PrintersForAnts/Mini-AfterSherpa/mods/LGXLiteMount/Strain_Relief_Spacers_x2.stl

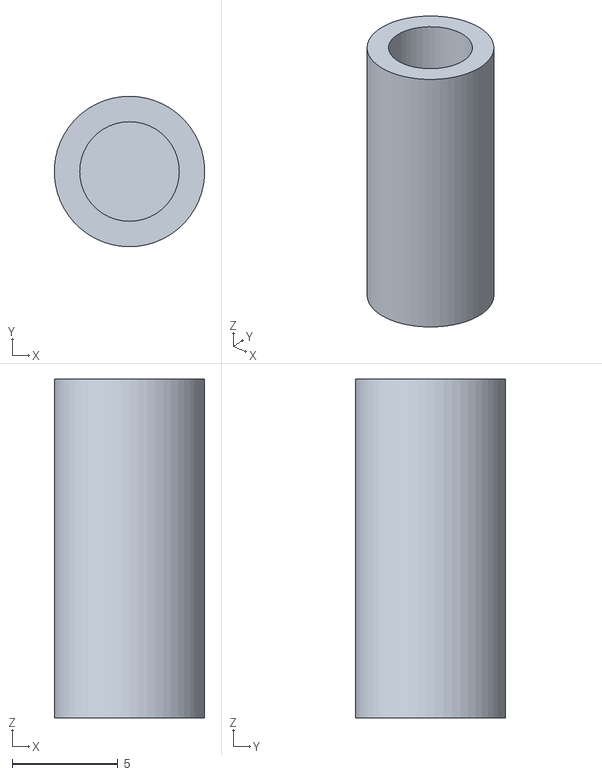
[picture p28: CAD file, 2022-01-24]
mods/LGXLiteMount/Strain_Relief_Spacers_x2.stl
7.09 x 7.10 x 16.0
