PrintersForAnts/Mini-AfterSherpa/STL/Mini_AfterSherpa/E3D_Revo_Micro_Toolhead/MiniAS_Revo_Micro_Shim_V2_x1.stl

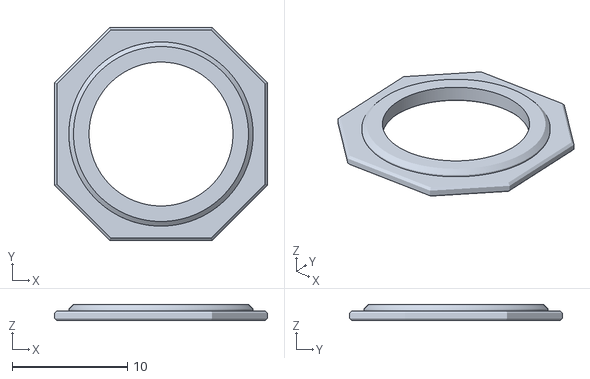
[picture p29: CAD file, 2022-02-25]
STL/Mini_AfterSherpa/E3D_Revo_Micro_Toolhead/MiniAS_Revo_Micro_Shim_V2_x1.stl
18.5 x 18.5 x 1.40
