PrintersForAnts/Mini-AfterSherpa/STL/Mini_AfterSherpa/E3D_V6_Zodiac_BMO_Toolhead/Mount_E3D_V6_x1.stl

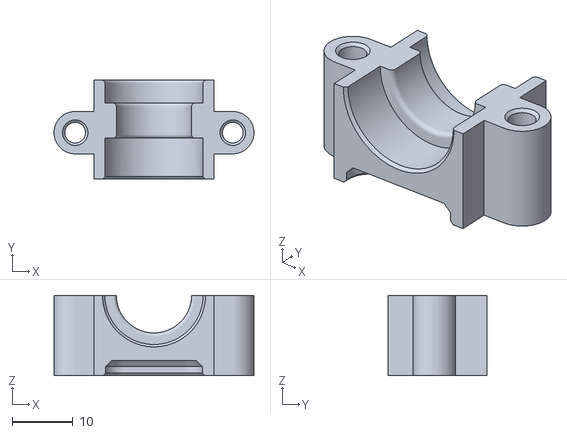
[picture p30: CAD file, 2021-11-07]
STL/Mini_AfterSherpa/E3D_V6_Zodiac_BMO_Toolhead/Mount_E3D_V6_x1.stl
33.0 x 16.4 x 13.3
