PrintersForAnts/Mini-AfterSherpa/STL/Mini_AfterSherpa/MiniAS_Sherpa_Micro_Adapter.stl

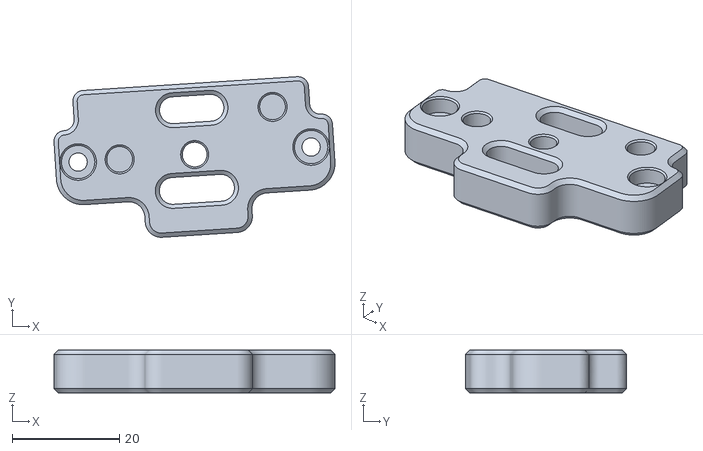
[picture p31: CAD file, 2022-04-30]
STL/Mini_AfterSherpa/MiniAS_Sherpa_Micro_Adapter.stl
52.4 x 29.9 x 8.00
