PrintersForAnts/Mini-AfterSherpa/STL/Mini_AfterSherpa/Orbiter_V2_Toolhead_ONE-OFFS/Mini_AfterSherpa_Orbiter_v2_X_Carriage.stl

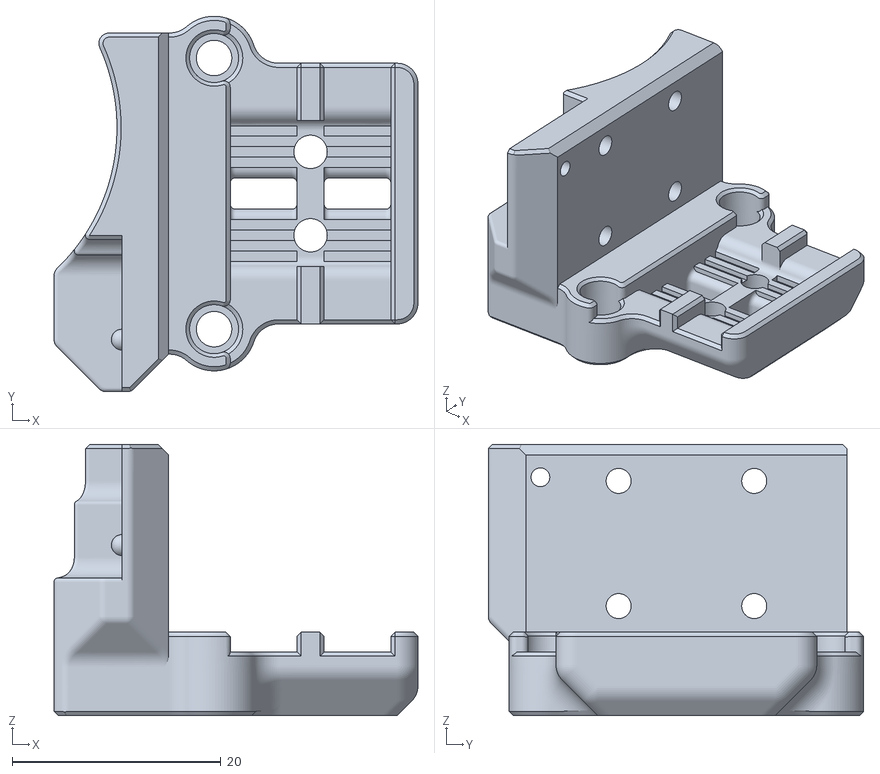
[picture p32: CAD file, 2022-04-30]
STL/Mini_AfterSherpa/Orbiter_V2_Toolhead_ONE-OFFS/Mini_AfterSherpa_Orbiter_v2_X_Carriage.stl
34.9 x 36.0 x 26.0
