PrintersForAnts/Mini-AfterSherpa/STL/Reversed_PocketWatch2/Reversed_Pocketwatch2_Mini_AS_Edition_v0.593/Motor_Mount_Rear_rP2_x1.stl

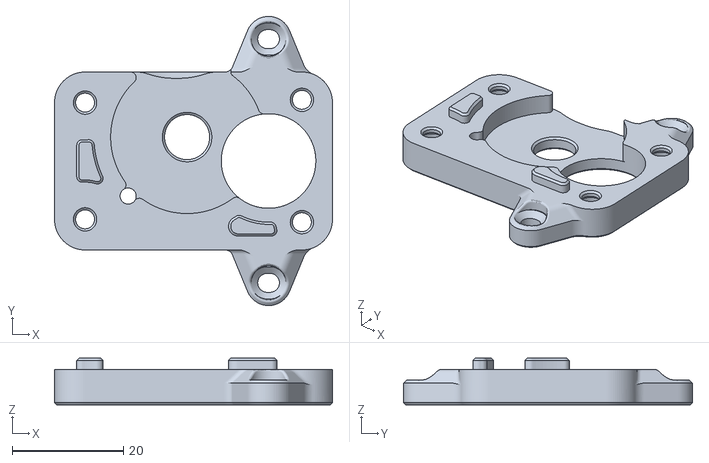
[picture p33: CAD file, 2021-11-07]
STL/Reversed_PocketWatch2/Reversed_Pocketwatch2_Mini_AS_Edition_v0.593/Motor_Mount_Rear_rP2_x1.stl
50.0 x 52.0 x 8.40
