PrintersForAnts/Mini-AfterSherpa/CAD/Mini-AfterSherpa_Zodiac_BMS.step

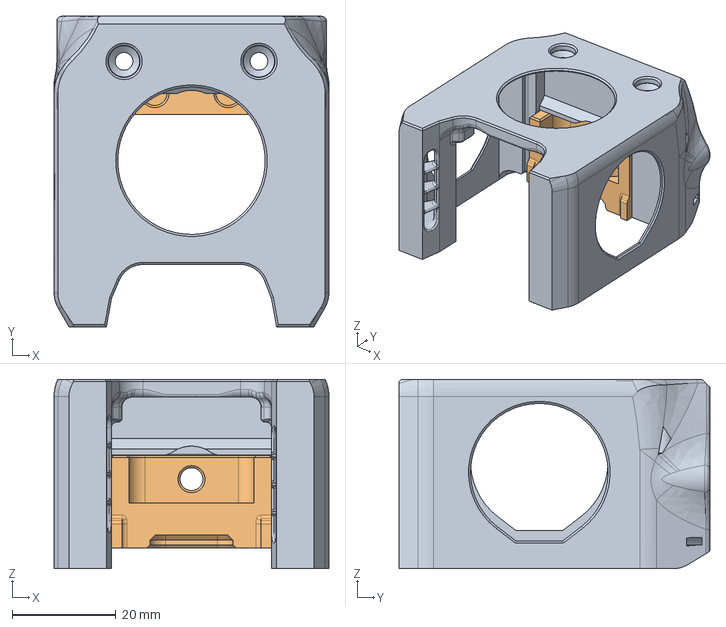
[picture p34: CAD file, 2022-04-30]
CAD/Mini-AfterSherpa_Zodiac_BMS.step
53.0 x 59.9 x 36.5 mm
