PrintersForAnts/Mini-AfterSherpa/mods/LED-Bowden-Adapter/led_logo_diffuser.stl

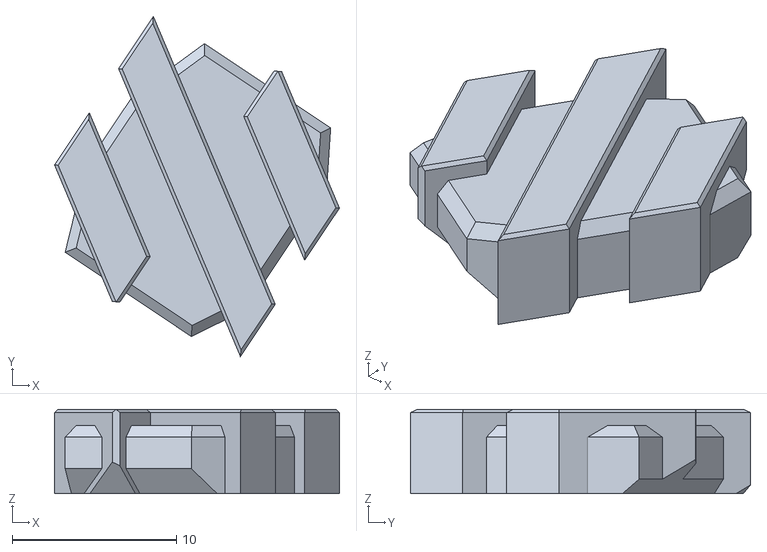
[picture p35: CAD file, 2022-01-20]
mods/LED-Bowden-Adapter/led_logo_diffuser.stl
17.3 x 20.7 x 5.13
