PrintersForAnts/Mini-AfterSherpa/mods/LGXLiteMount/MiniASLGXerpaLite-StrainRelief.stl

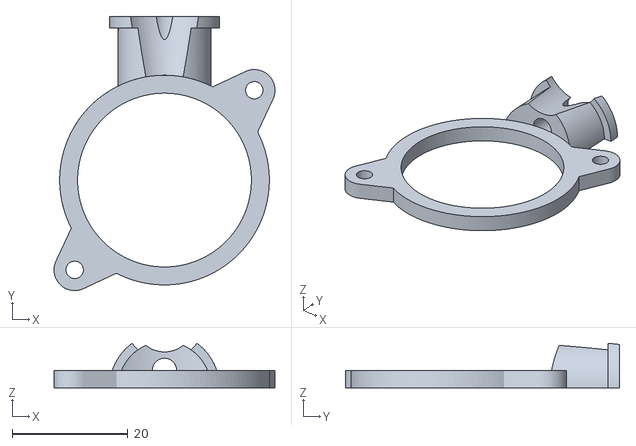
[picture p36: CAD file, 2022-01-24]
mods/LGXLiteMount/MiniASLGXerpaLite-StrainRelief.stl
38.2 x 47.3 x 7.69
