PrintersForAnts/Mini-AfterSherpa/STL/Mini_AfterSherpa/E3D_Revo_Micro_Toolhead/MiniAS_Revo_Micro_Faux_Collet_V2_X1.stl

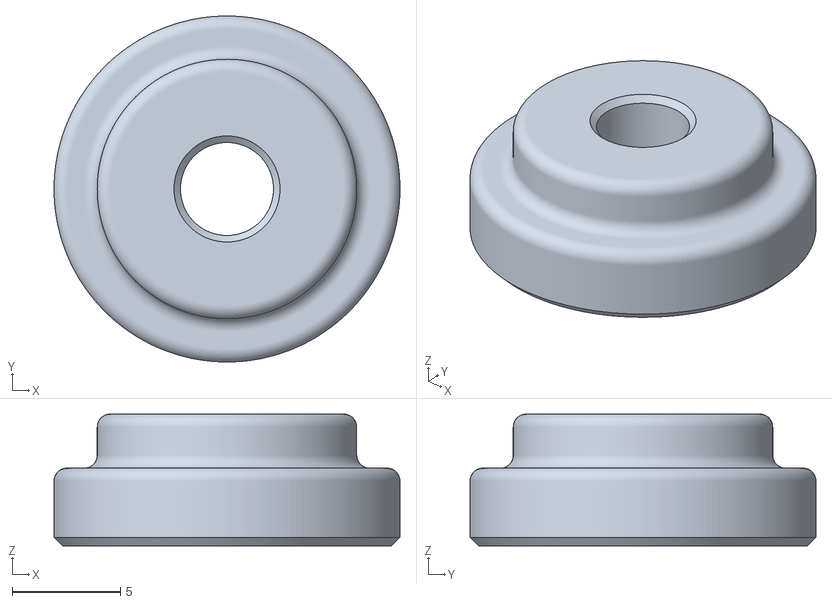
[picture p37: CAD file, 2022-02-25]
STL/Mini_AfterSherpa/E3D_Revo_Micro_Toolhead/MiniAS_Revo_Micro_Faux_Collet_V2_X1.stl
16.0 x 16.0 x 6.10
