PrintersForAnts/Mini-AfterSherpa/STL/Mini_AfterSherpa/MiniAS_Orbiter_v1.5_Adapter.stl

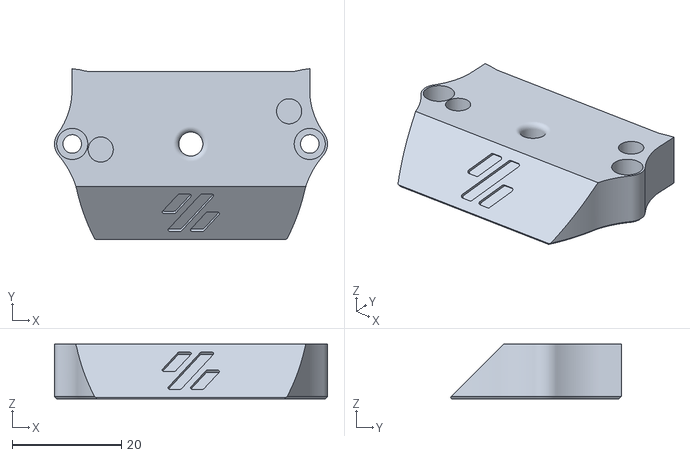
[picture p38: CAD file, 2022-02-27]
STL/Mini_AfterSherpa/MiniAS_Orbiter_v1.5_Adapter.stl
50.0 x 31.3 x 10.0
