PrintersForAnts/Mini-AfterSherpa/STL/Mini_AfterSherpa/Orbiter_V2_Toolhead_ONE-OFFS/Orbiter v2.0 cable support.stl

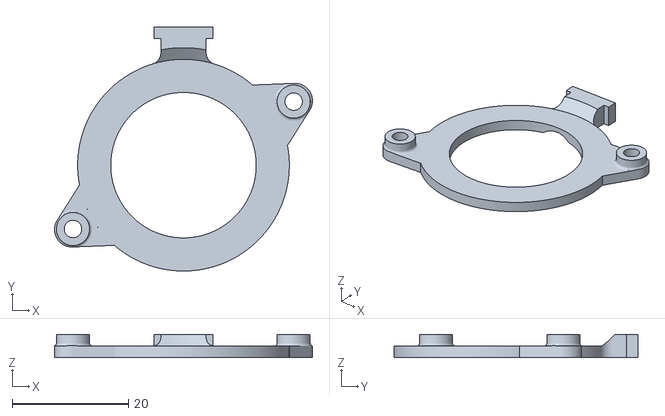
[picture p39: CAD file, 2022-02-23]
STL/Mini_AfterSherpa/Orbiter_V2_Toolhead_ONE-OFFS/Orbiter v2.0 cable support.stl
44.4 x 42.0 x 4.00
