PrintersForAnts/Mini-AfterSherpa/STL/Reversed_PocketWatch2/Reversed_Pocketwatch2_Mini_AS_Edition_v0.593/[a]_Guidler_rP2_x1.stl

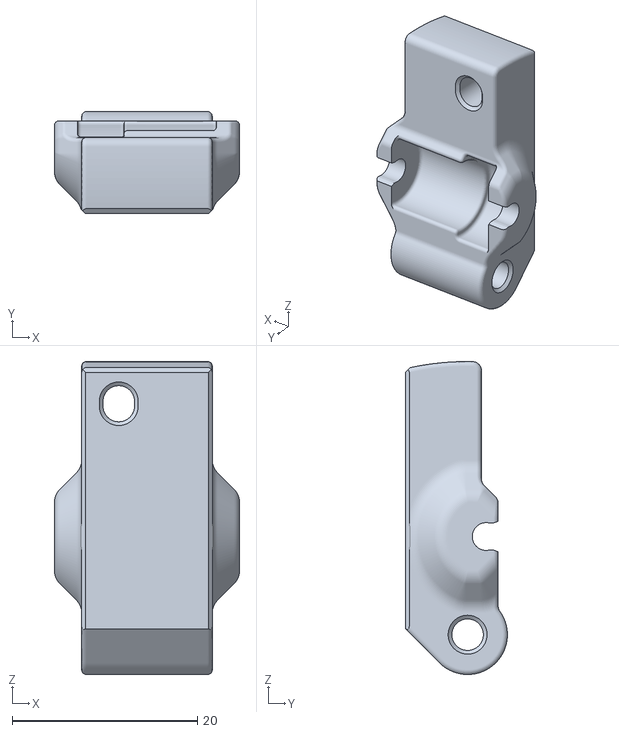
[picture p40: CAD file, 2021-11-07]
STL/Reversed_PocketWatch2/Reversed_Pocketwatch2_Mini_AS_Edition_v0.593/[a]_Guidler_rP2_x1.stl
20.0 x 11.0 x 33.8
