PrintersForAnts/Mini-AfterSherpa/mods/LED-Bowden-Adapter/pcb_cover.stl

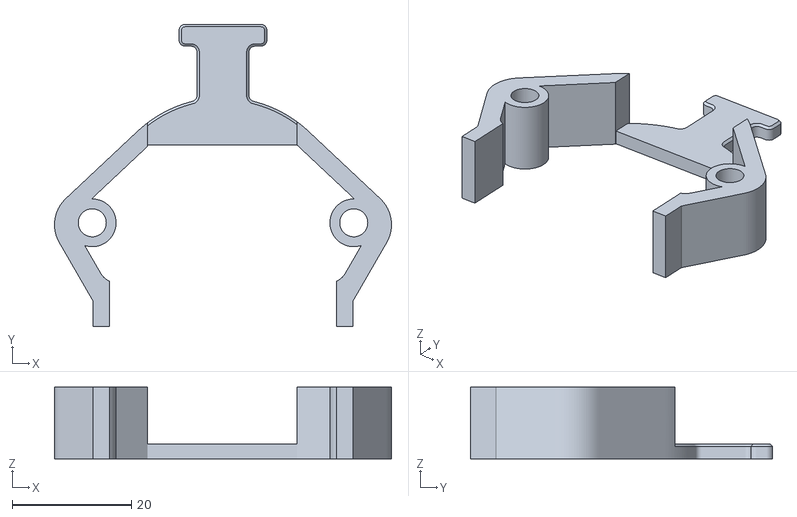
[picture p41: CAD file, 2022-01-20]
mods/LED-Bowden-Adapter/pcb_cover.stl
56.5 x 50.7 x 12.0
