PrintersForAnts/Mini-AfterSherpa/mods/LGXLiteMount/MiniASLGXerpaLite-Cover.stl

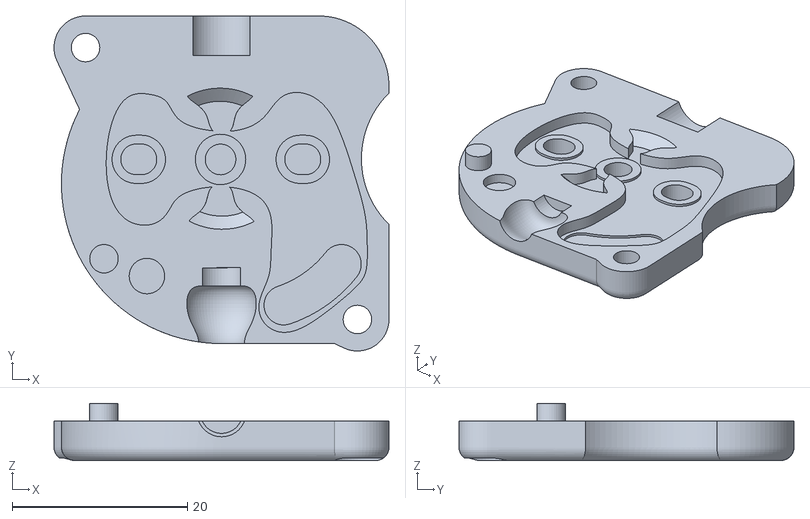
[picture p42: CAD file, 2022-01-24]
mods/LGXLiteMount/MiniASLGXerpaLite-Cover.stl
38.2 x 38.2 x 6.50
