PrintersForAnts/Mini-AfterSherpa/STL/Reversed_PocketWatch2/Reversed_Pocketwatch2_Mini_AS_Edition_v0.593/Guts_rP2_front_x1.stl

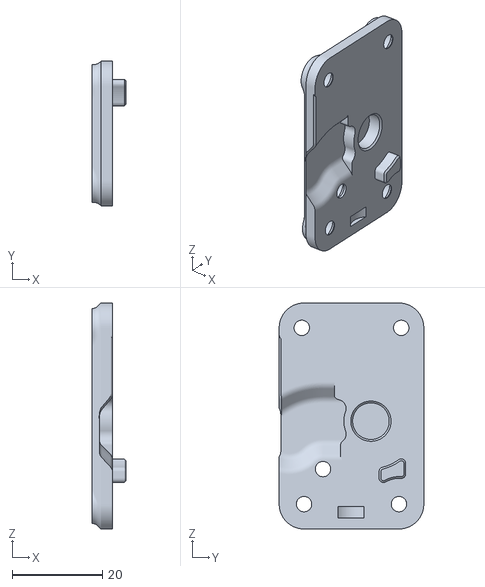
[picture p43: CAD file, 2021-11-07]
STL/Reversed_PocketWatch2/Reversed_Pocketwatch2_Mini_AS_Edition_v0.593/Guts_rP2_front_x1.stl
7.57 x 32.0 x 50.0
