PrintersForAnts/Mini-AfterSherpa/mods/LED-Bowden-Adapter/logo_led_carrier.stl

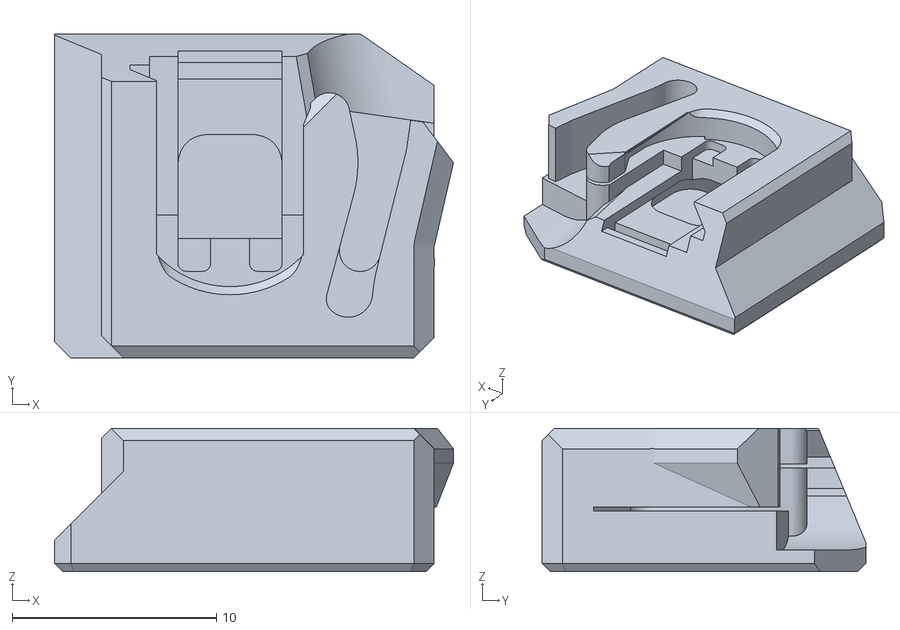
[picture p44: CAD file, 2022-01-20]
mods/LED-Bowden-Adapter/logo_led_carrier.stl
19.5 x 15.9 x 7.01
