PrintersForAnts/Mini-AfterSherpa/STL/Reversed_PocketWatch2/Reversed_Pocketwatch2_Mini_AS_Edition_v0.593/[a]_Latch_Shuttle_rP2_x1.stl

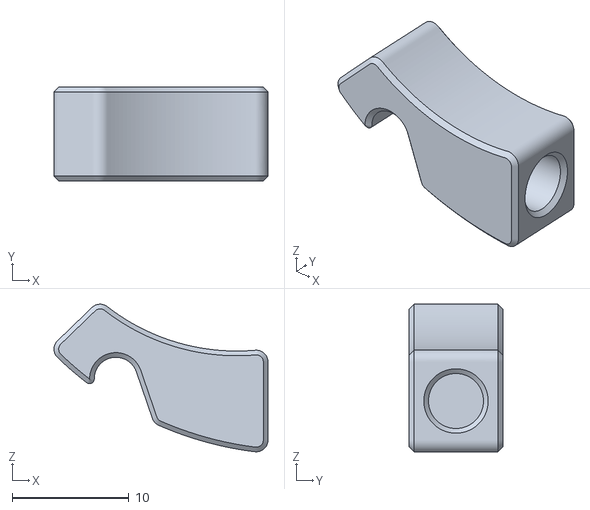
[picture p45: CAD file, 2021-11-07]
STL/Reversed_PocketWatch2/Reversed_Pocketwatch2_Mini_AS_Edition_v0.593/[a]_Latch_Shuttle_rP2_x1.stl
18.3 x 8.00 x 12.6
