PrintersForAnts/Mini-AfterSherpa/STL/Reversed_PocketWatch2/Reversed_Pocketwatch2_Mini_AS_Edition_v0.593/Motor_Mount_Front_rP2_x1.stl

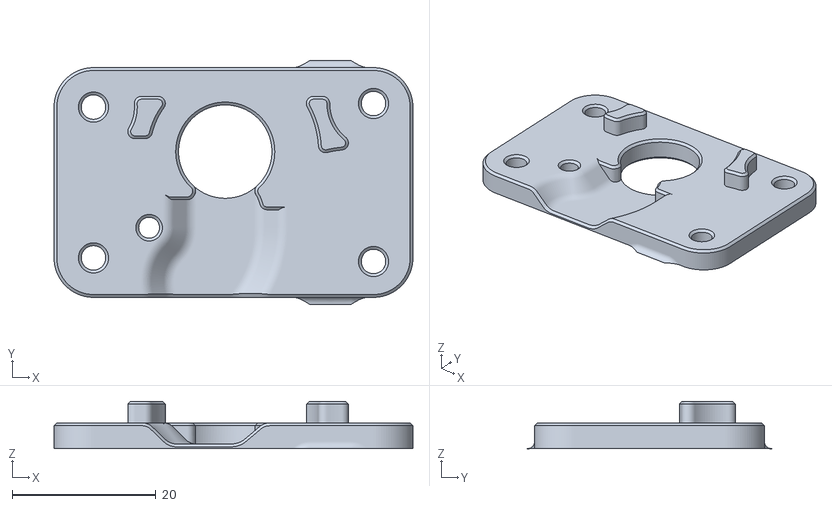
[picture p46: CAD file, 2021-11-07]
STL/Reversed_PocketWatch2/Reversed_Pocketwatch2_Mini_AS_Edition_v0.593/Motor_Mount_Front_rP2_x1.stl
50.0 x 34.0 x 6.60
